TharushaNimesh22/IRON-GENIUS/Images/Final Product 3.png

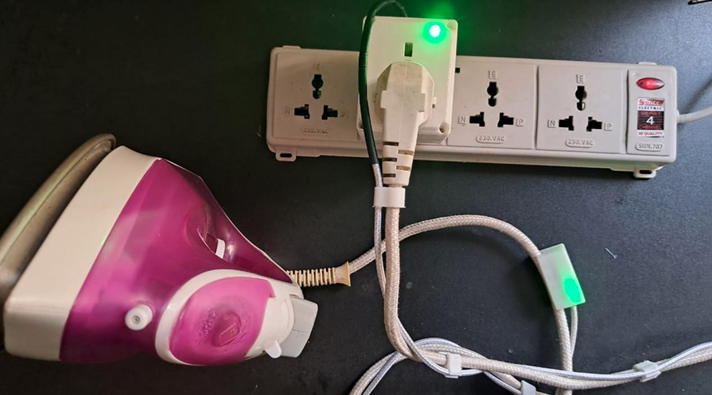
Images/Final Product 3.png
