TharushaNimesh22/IRON-GENIUS/Images/Final product.png

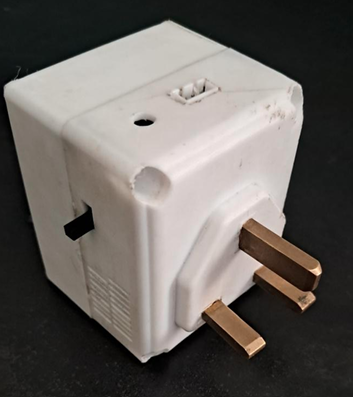
Images/Final product.png
