TharushaNimesh22/IRON-GENIUS/Images/PCB.png

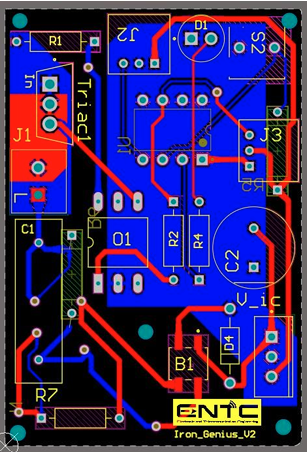
Images/PCB.png
