TharushaNimesh22/IRON-GENIUS/Images/Screenshot 2025-07-09 161653.png

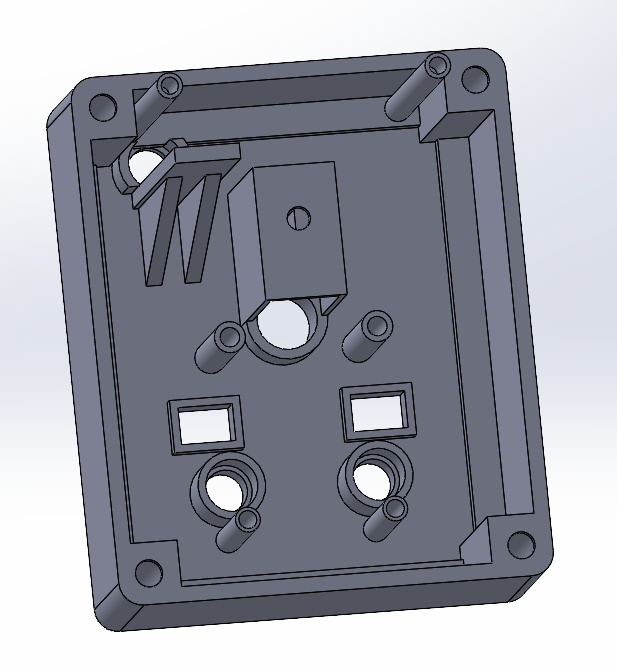
Images/Screenshot 2025-07-09 161653.png
